tg257225-oss/Nahoboard/Assets/wiringwip.png

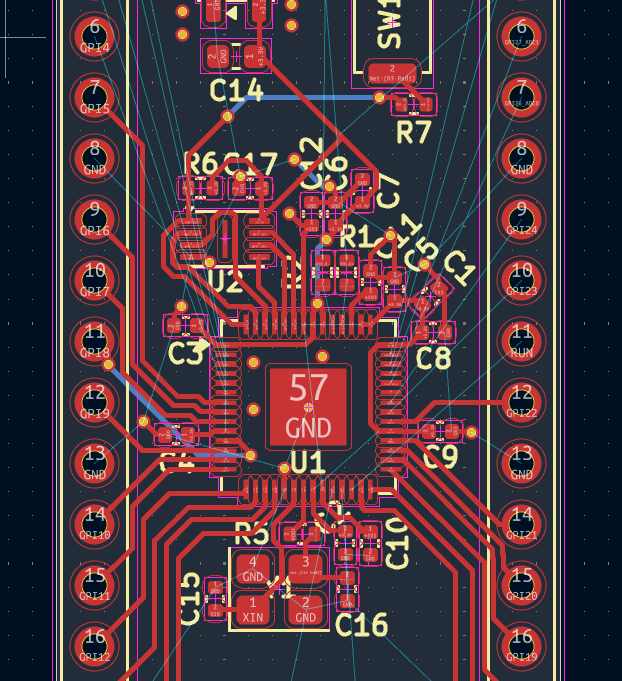
Assets/wiringwip.png
